petnica-rac-seminari/BCD-0o27-Tetris/firmware/framework/data/start_screen.jpeg

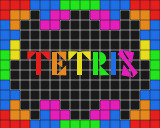
firmware/framework/data/start_screen.jpeg
