petnica-rac-seminari/BCD-0o27-Tetris/firmware/framework/data/a.jpeg

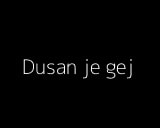
firmware/framework/data/a.jpeg
