petnica-rac-seminari/BCD-0o27-Tetris/firmware/framework/data/end_screen.jpeg

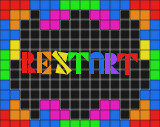
firmware/framework/data/end_screen.jpeg
