petnica-rac-seminari/BCD-0o27-Tetris/firmware/framework/src/board.cpp

#include <freertos/mpu_wrappers.h>
#include <cstdlib>
#include "board.h"
#include <freertos/projdefs.h>

namespace tetrics_module
{
	void board::start()
	{
        downDifMS = 500;		
		score = 0;
		currentRotation = 0;
		inc = 0;
		
		nextShapeColor = rand() % 6 + 1;
		nextShapeIndex = rand() % 7;
		nextShape = getShape(nextShapeIndex, currentRotation);

		clear();
		createShape();

	}
	bool board::frame(TickType_t currtick)
	{		
		TickType_t downDif = pdMS_TO_TICKS(downDifMS);

		if (downDif <= currtick - lastTick)
		{
			if (checkCollision())
				moveDown();
			else
				return createShape();

			lastTick = currtick;
		}
		
		return true;
	}
	int board::getDropCoordinate()
	{
		for (int k = 0; k < height; ++k)
			for (int i = 0; i < 4; i++)
				for (int j = 0; j < 4; j++)
					if (currentShape[i][j] < 0 && (k + j + 1 >= height || board[currentShapeX + i][k + j + 1] > 0))
						return k;

		return 0;
	}
	void board::drop(TickType_t currTick)
	{
		for (int j = std::min(currentShapeY + 3, height - 1); j >= std::max(currentShapeY, 0); j--)
			for (int i = std::max(currentShapeX, 0); i < std::min(currentShapeX + 4, width); i++)
				if (board[i][j] < 0)
					board[i][j] = 0;
		
		currentShapeY = getDropCoordinate();

		for (int j = std::min(currentShapeY + 3, height - 1); j >= std::max(currentShapeY, 0); j--)
			for (int i = std::max(currentShapeX, 0); i < std::min(currentShapeX + 4, width); i++)
				if (currentShape[i - currentShapeX][j - currentShapeY] < 0)
					board[i][j] = -currentShapeColor;

		lastTick = currTick - pdMS_TO_TICKS(downDifMS);
	}
	void board::clear()
	{
		for (int i = 0; i < width; i++)
			for (int j = 0; j < height; j++)
				board[i][j] = 0;
	}	
	void board::rotate()
	{		
		std::array<std::array<int, 4>, 4> rotatedShape = getShape(shapeIndex, (currentRotation + 1) % 4);

		for (int i = currentShapeX; i < currentShapeX + 4; i++)
			for (int j = currentShapeY; j < currentShapeY + 4; j++)
				if (rotatedShape[i - currentShapeX][j - currentShapeY] < 0 && (i < 0 || i >= width || j < 0 || j >= height || board[i][j] > 0))
					return;

		currentRotation = (currentRotation + 1) % 4;
		currentShape = rotatedShape;

		for (int i = std::max(currentShapeX, 0); i < std::min(currentShapeX + 4, width); i++)
			for (int j = std::max(currentShapeY, 0); j < std::min(currentShapeY + 4, height); j++)
			{
				if(board[i][j] < 0) 
					board[i][j] = 0;

				if(currentShape[i - currentShapeX][j - currentShapeY] < 0)
					board[i][j] = -currentShapeColor;
			}
	}	
	bool board::createShape()
	{
		currentShapeX = rand() % 7;
		currentShapeY = 0;
		currentRotation = 0;
		currentShape = nextShape;
		currentShapeColor = nextShapeColor;
		shapeIndex = nextShapeIndex;

		nextShapeColor = rand() % 6 + 1;
		nextShapeIndex = rand() % 7;
		nextShape = getShape(nextShapeIndex, currentRotation);		

		for (int i = std::max(currentShapeX, 0); i < std::min(currentShapeX + 4, width); i++)		
			for (int j = std::max(currentShapeY, 0); j < std::min(currentShapeY + 4, height); j++)
			{
				if (currentShape[i - currentShapeX][j - currentShapeY] < 0 && board[i][j] != 0)
					return false;

				if (currentShape[i - currentShapeX][j - currentShapeY] < 0)
					board[i][j] = -currentShapeColor;
			}
		
		return true;
	}
	void board::moveRight()
	{
		for (int i = std::max(currentShapeX, 0); i < std::min(currentShapeX + 4, width); i++)
			for (int j = std::max(currentShapeY, 0); j < std::min(currentShapeY + 4, height); j++)
				if (board[i][j] < 0 && (i + 1 == width || board[i + 1][j] > 0))
					return;

		for (int i = std::min(currentShapeX + 3, width - 1); i >= std::max(currentShapeX, 0); i--)
			for (int j = std::max(currentShapeY, 0); j < std::min(currentShapeY + 4, height); j++)
				if (board[i][j] < 0)
				{
					board[i + 1][j] = board[i][j];
					board[i][j] = 0;
				}

		currentShapeX += 1;
	}
	void board::moveLeft()
	{
		for (int i = std::max(currentShapeX, 0); i < std::min(currentShapeX + 4, width); i++)
			for (int j = std::max(currentShapeY, 0); j < std::min(currentShapeY + 4, height); j++)
				if (board[i][j] < 0 && (i == 0 || board[i - 1][j] > 0))
					return;
				
		for (int i = std::max(currentShapeX, 0); i < std::min(currentShapeX + 4, width); i++)
			for (int j = std::max(currentShapeY, 0); j < std::min(currentShapeY + 4, height); j++)
				if (board[i][j] < 0) 
				{
					board[i - 1][j] = board[i][j];
					board[i][j] = 0;
				}

		currentShapeX -= 1;
	}
	void board::moveDown()
	{
		for (int i = std::max(currentShapeX, 0); i < std::min(currentShapeX + 4, width); i++)
			for (int j = std::max(currentShapeY, 0); j < std::min(currentShapeY + 4, height); j++)
				if (board[i][j] < 0 && (j + 1 == height || board[i][j + 1] > 0))
					return;

		for (int j = std::min(currentShapeY + 3, height - 1); j >= std::max(currentShapeY, 0); j--)
			for (int i = std::max(currentShapeX, 0); i < std::min(currentShapeX + 4, width); i++)
				if (board[i][j] < 0)
				{
					board[i][j + 1] = board[i][j];
					board[i][j] = 0;
				}
			
		currentShapeY += 1;
	}
	bool board::checkCollision()
	{
		bool canMove = true;

		for (int i = std::max(currentShapeX, 0); i < std::min(currentShapeX + 4, width); i++)
		{
			for (int j = std::max(currentShapeY, 0); j < std::min(currentShapeY + 4, height); j++)
				if (board[i][j] < 0 && (j + 1 == height || board[i][j + 1] > 0))				
				{
					canMove = false;
					break;
				}
			
			if (!canMove)
				break;
		}

		if (canMove)
			return true;

		updateScore(4);

		for (int i = std::max(currentShapeX, 0); i < std::min(currentShapeX + 4, width); i++)
			for (int j = std::max(currentShapeY, 0); j < std::min(currentShapeY + 4, height); j++)
				if (board[i][j] < 0)
					board[i][j] = -board[i][j];
	
		for (int j = height - 1; j >= 0; j--)
		{
			int numOfBlocks = 0;
			for (int i = 0; i < width; i++)
			{
				if (board[i][j] > 0)
					numOfBlocks++;
			}

				if (numOfBlocks == width)
				{
					updateScore(10);
					for (int k = j; k > 0; k--)
						for (int i = 0; i < width; i++)
							board[i][k] = board[i][k - 1];

					for (int i = 0; i < width; i++)
						board[i][0] = 0;

					j++;
				}
			}
			
			for (int i = std::max(currentShapeX, 0); i < std::min(currentShapeX + 4, width); i++)
				for (int j = std::max(currentShapeY, 0); j < std::min(currentShapeY + 4, height); j++)
					if (board[i][j] < 0)
						board[i][j] = -board[i][j];

		return false;
	}	
	void board::updateScore(int increase) {
		score += increase;
		inc += increase;
		if(inc > 10 && downDifMS >= speedUp) {
			downDifMS -= speedUp;
			inc = 0;
		}
	}
	board::piece board::getShape(int shapeIndex, int rotation)
	{
		switch (shapeIndex)
		{
		case 0: return I_shape[rotation];
		case 1: return L_shape[rotation];
		case 2: return J_shape[rotation];
		case 3: return Z_shape[rotation];
		case 4: return T_shape[rotation];
		case 5: return S_shape[rotation];
		case 6: return O_shape[rotation];
		}

		return { { } };
	}	
}
