petnica-rac-seminari/BCD-0o27-Tetris/firmware/framework/src/graphics.cpp

/*#include "main.hpp"

void Main::drawStartScreen()
{
    // draw::image("start_screen.png", 0, 0);
}

void Main::drawGameScreen()
{
    // draw::
}

void Main::drawEndScreen()
{
    // draw::image("end_screen.png", 0, 0);
}*/
